Fu-Xiaotian/20_key_RGBKeyboard/Arduino_code/Source/keydefine.cpp

#include "RGBkeyboard.h"

const KeyboardKeycode key_layer[20][20] = {
	//1
	{KEY_1,KEY_2,KEY_3,KEY_4,
	KEY_Q,KEY_W,KEY_E,KEY_R,
	KEY_A,KEY_S,KEY_D,KEY_F,
	KEY_Z,KEY_B,KEY_LEFT_CTRL,KEY_TAB,
	KEY_FN,KEY_G,KEY_LEFT_SHIFT,KEY_SPACE},
	//2
	{KEY_TAB,KEY_PERIOD,KEY_3,KEY_4,
	KEY_Q,KEY_W,KEY_E,KEY_R,
	KEY_A,KEY_S,KEY_D,KEY_F,
	KEY_LEFT_SHIFT,KEY_Z,KEY_X,KEY_LEFT_ALT,
	KEY_LEFT_CTRL,KEY_B,KEY_C,KEY_SPACE},
	//3
	{KEY_NUM_LOCK,KEYPAD_DIVIDE,KEYPAD_MULTIPLY,KEYPAD_SUBTRACT,
	KEYPAD_7,KEYPAD_8,KEYPAD_9,KEYPAD_ADD,
	KEYPAD_4,KEYPAD_5,KEYPAD_6,KEY_BACKSPACE,
	KEYPAD_1,KEYPAD_2,KEYPAD_3,KEY_TAB,
	KEY_FN,KEYPAD_0,KEYPAD_DOT,KEY_RETURN},
	//4
	{KEY_NUM_LOCK,KEYPAD_DIVIDE,KEYPAD_MULTIPLY,KEYPAD_SUBTRACT,
	KEYPAD_7,KEYPAD_8,KEYPAD_9,KEYPAD_ADD,
	KEYPAD_4,KEYPAD_5,KEYPAD_6,KEY_BACKSPACE,
	KEYPAD_1,KEYPAD_2,KEYPAD_3,KEY_TAB,
	KEY_FN,KEYPAD_0,KEYPAD_DOT,KEY_RETURN},
	//5
	{KEY_NUM_LOCK,KEYPAD_DIVIDE,KEYPAD_MULTIPLY,KEYPAD_SUBTRACT,
	KEYPAD_7,KEYPAD_8,KEYPAD_9,KEYPAD_ADD,
	KEYPAD_4,KEYPAD_5,KEYPAD_6,KEY_BACKSPACE,
	KEYPAD_1,KEYPAD_2,KEYPAD_3,KEY_TAB,
	KEY_FN,KEYPAD_0,KEYPAD_DOT,KEY_RETURN},
	//6
	{KEY_NUM_LOCK,KEYPAD_DIVIDE,KEYPAD_MULTIPLY,KEYPAD_SUBTRACT,
	KEYPAD_7,KEYPAD_8,KEYPAD_9,KEYPAD_ADD,
	KEYPAD_4,KEYPAD_5,KEYPAD_6,KEY_BACKSPACE,
	KEYPAD_1,KEYPAD_2,KEYPAD_3,KEY_TAB,
	KEY_FN,KEYPAD_0,KEYPAD_DOT,KEY_RETURN},
	//7
	{KEY_NUM_LOCK,KEYPAD_DIVIDE,KEYPAD_MULTIPLY,KEYPAD_SUBTRACT,
	KEYPAD_7,KEYPAD_8,KEYPAD_9,KEYPAD_ADD,
	KEYPAD_4,KEYPAD_5,KEYPAD_6,KEY_BACKSPACE,
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
	KEY_FN,KEYPAD_0,KEYPAD_DOT,KEY_RETURN},
	//20
	{KEY_NUM_LOCK,KEYPAD_DIVIDE,KEYPAD_MULTIPLY,KEYPAD_SUBTRACT,
	KEYPAD_7,KEYPAD_8,KEYPAD_9,KEYPAD_ADD,
	KEYPAD_4,KEYPAD_5,KEYPAD_6,KEY_BACKSPACE,
	KEYPAD_1,KEYPAD_2,KEYPAD_3,KEY_TAB,
	KEY_FN,KEYPAD_0,KEYPAD_DOT,KEY_RETURN}
};
