Fu-Xiaotian/20_key_RGBKeyboard/Arduino_code/Source/macro.h

#ifndef __MACRO_H
#define __MACRO_H

extern int macro_flag;

long get_macro_delay(void);

void Macro_Switch(void);
void Key_0_MARCO(void);
void Key_1_MARCO(void);
void Key_2_MARCO(void);
void Key_3_MARCO(void);
void Key_4_MARCO(void);
void Key_5_MARCO(void);
void Key_6_MARCO(void);
void Key_7_MARCO(void);
void Key_8_MARCO(void);
void Key_9_MARCO(void);
void Key_10_MARCO(void);
void Key_11_MARCO(void);
void Key_12_MARCO(void);
void Key_13_MARCO(void);
void Key_14_MARCO(void);
void Key_15_MARCO(void);
void Key_16_MARCO(void);
void Key_17_MARCO(void);
void Key_18_MARCO(void);
void Key_19_MARCO(void);

#define RUN_ONCE macro_flag = -1

#endif
