Fu-Xiaotian/20_key_RGBKeyboard/Arduino_code/Source/Setting.h

#ifndef __SETTING_H
#define __SETTING_H

#define DEBOUNCETIME 10 //键盘消抖延时，单位ms
#define BRIGHTNESS 32 //默认灯光亮度，0~128取值
#define SLEEP_TIME 5*60*1000UL //定义休眠时间，单位ms
#define FADE_OUT_SPEED 2 //单点亮灯光模式渐隐速度，建议1~10取值

#endif
